alexf91/WSPR-Beacon/hardware/filters/filter_20m.asc

C1: cap; 220p
C2: cap; 390p
C3: cap; 390p
C4: cap; 220p
L1: ind; 0.75µ
L2: ind; 0.91µ
L3: ind; 0.75µ
V1: voltage; ""; AC 1
Named nets: 0
.ac dec 100 1Meg 60Meg
