alexf91/WSPR-Beacon/hardware/filters/filter_30m.asc

C1: cap; 300p
C2: cap; 560p
C3: cap; 560p
C4: cap; 300p
L1: ind; 1µ
L2: ind; 1µ2
L3: ind; 1µ
V1: voltage; ""; AC 1
Named nets: 0
.ac dec 100 1Meg 30Meg
