alexf91/WSPR-Beacon/hardware/filters/filter_40m.asc

C1: cap; 430p
C2: cap; 820p
C3: cap; 820p
C4: cap; 430p
L1: ind; 1µ5
L2: ind; 1µ8
L3: ind; 1µ5
V1: voltage; ""; AC 1
Named nets: 0
.ac dec 100 1Meg 30Meg
